make-Div-meter/Div-meter/nixie/200VDCDC/200VDCDC.sch

## KiCad design nixie/200VDCDC/200VDCDC.sch (2020-03-31)

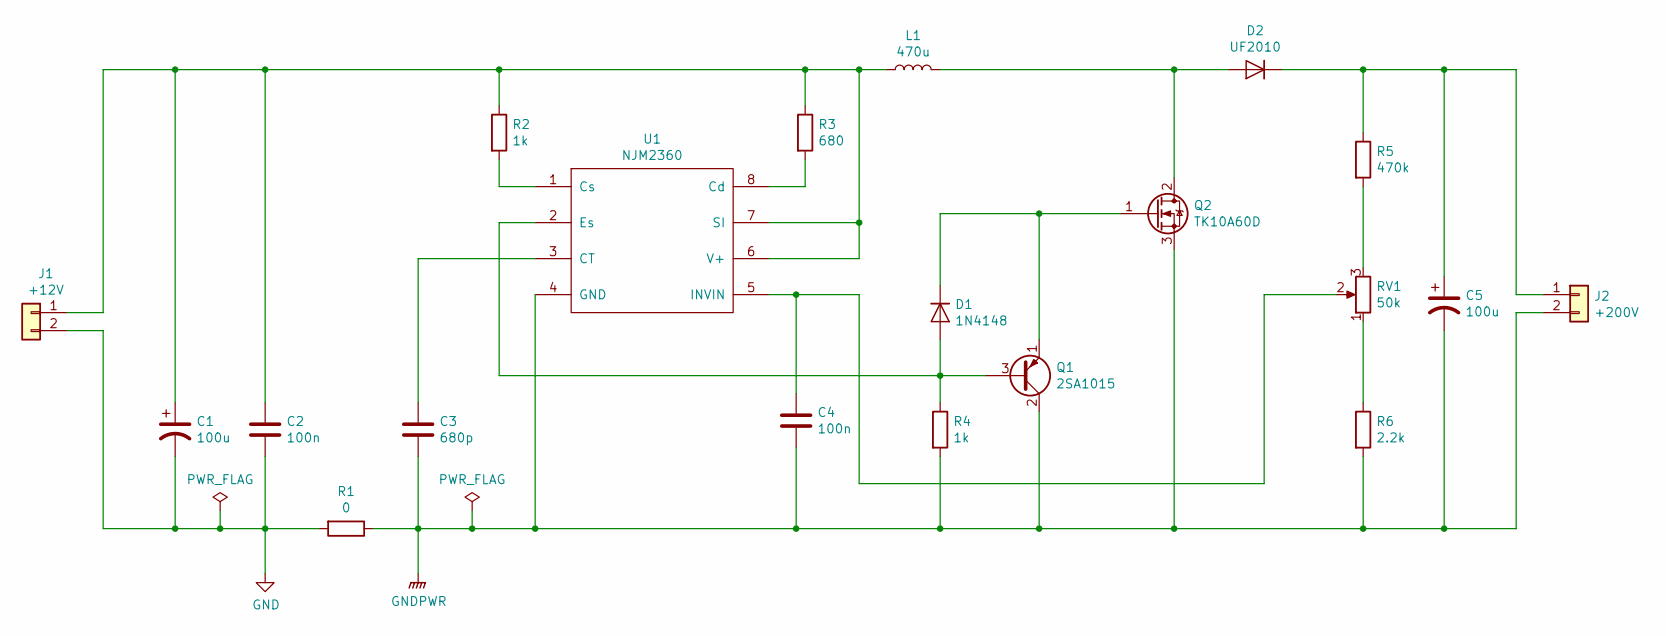
[picture p5: schematic 200VDCDC.sch]

Parts:
C1: 100u; CP_Elec_10x12.5
C2, C4: 100n; C_0603_1608Metric_Pad1.05x0.95mm_HandSolder
C3: 680p; C_0603_1608Metric_Pad1.05x0.95mm_HandSolder
C5: 100u; CP_Radial_D18.0mm_P7.50mm
D1: 1N4148; D_A-405_P7.62mm_Horizontal
D2: UF2010; D_T-1_P10.16mm_Horizontal
J1: +12V; PinHeader_1x02_P2.54mm_Vertical
J2: +200V; PinHeader_1x02_P2.54mm_Vertical
L1: 470u; L_12x12mm_H8mm
Q1: 2SA1015; TO-92_Inline_Wide
Q2: TK10A60D; TO-3PB-3_Vertical
R1: 0; R_0603_1608Metric_Pad1.05x0.95mm_HandSolder
R2, R4: 1k; R_0603_1608Metric_Pad1.05x0.95mm_HandSolder
R3: 680; R_0603_1608Metric_Pad1.05x0.95mm_HandSolder
R5: 470k; R_0603_1608Metric_Pad1.05x0.95mm_HandSolder
R6: 2.2k; R_0603_1608Metric_Pad1.05x0.95mm_HandSolder
RV1: 50k; Potentiometer_ACP_CA6-H2,5_Horizontal
U1: NJM2360; DIP-8_W8.89mm_SMDSocket_LongPads

Connections:
GND: C1.2, C2.2, J1.2, R1.2
GNDPWR: C3.2, C4.2, C5.2, J2.2, Q1.2 (C), Q2.3 (S), R1.1, R4.2, R6.2, U1.4 (GND)
unnamed: C1.1, C2.1, J1.1, L1.1, R2.1, R3.1, U1.6 (V+), U1.7 (SI)
unnamed: C3.1, U1.3 (CT)
unnamed: C4.1, RV1.2, U1.5 (INVIN)
unnamed: C5.1, D2.1 (K), J2.1, R5.1
unnamed: D1.1 (K), Q1.1 (E), Q2.1 (G)
unnamed: D1.2 (A), Q1.3 (B), R4.1, U1.2 (Es)
unnamed: D2.2 (A), L1.2, Q2.2 (D)
unnamed: R2.2, U1.1 (Cs)
unnamed: R3.2, U1.8 (Cd)
unnamed: R5.2, RV1.3
unnamed: R6.1, RV1.1
